kollero/Soldering-station/code/SRC/Thermotable.h

uint16_t Etype100amp[][2]={
{0,0},    
{12,10},  
{31,25},  
{50,40},  
{102,80}, 
{186,140},
{215,160},
{245,180},
{275,200},
{305,220},
{336,240},
{368,260},
{399,280},
{431,300},
{463,320},
{479,330},
{495,340},
{511,350},
{528,360},
{544,370},
{560,380},
{576,390},
{593,400},
{609,410},
{626,420},
{659,440},
{692,460},
{725,480},
{758,500}
};


//ADC value, then temperature calculated with gain of 100
uint16_t Ntype100amp[][2]={
{0,0},    
{13,25},  
{22,40},  
{45,80},  
{82,140}, 
{88,150}, 
{95,160}, 
{101,170},
{108,180},
{114,190},
{121,200},
{128,210},
{135,220},
{142,230},
{149,240},
{156,250},
{163,260},
{170,270},
{177,280},
{184,290},
{191,300},
{199,310},
{206,320},
{213,330},
{221,340},
{228,350},
{236,360},
{243,370},
{251,380},
{258,390},
{266,400},
{273,410},
{281,420},
{289,430},
{296,440},
{304,450},
{312,460},
{320,470},
{327,480},
{335,490},
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
};

uint16_t Ntype200amp[][2]={
{0,0},    
{27,25},  
{44,40},  
{90,80},  
{163,140},
{176,150},
{189,160},
{202,170},
{215,180},
{229,190},
{242,200},
{256,210},
{269,220},
{283,230},
{297,240},
{311,250},
{325,260},
{339,270},
{354,280},
{368,290},
{383,300},
{397,310},
{412,320},
{427,330},
{441,340},
{456,350},
{471,360},
{486,370},
{501,380},
{516,390},
{531,400},
{547,410},
{562,420},
{577,430},
{593,440},
{608,450},
{624,460},
{639,470},
{655,480},
{670,490},
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
};

//ADC value, C type then temperature calculated with gain of 500
//for 5V Vcc and 10-bit ADC, {adc,temp}
uint16_t Ctype500amp[][2]={
{0,0},    
{3,5},    
{18,25},  
{28,40},  
{59,80},  
{107,140},
{124,160},
{141,180},
{158,200},
{176,220},
{194,240},
{212,260},
{230,280},
{249,300},
{268,320},
{277,330},
{287,340},
{296,350},
{306,360},
{316,370},
{325,380},
{335,390},
{345,400},
{354,410},
{364,420},
{384,440},
{404,460},
{423,480},
{443,500}
};

uint16_t Stype1000amp[][2]={
{0,0},    
{11,10},  
{29,25},  
{48,40},  
{103,80}, 
{195,140},
{227,160},
{261,180},
{295,200},
{330,220},
{366,240},
{402,260},
{438,280},
{476,300},
{513,320},
{532,330},
{551,340},
{571,350},
{590,360},
{609,370},
{629,380},
{648,390},
{667,400},
{687,410},
{707,420},
{746,440},
{786,460},
{827,480},
{867,500}
};

uint16_t own500amp[][2]={
{0,25},   
{12,54},  
{34,99},  
{54,139}, 
{76,182}, 
{97,224}, 
{117,264},
{134,293},
{154,327},
{174,361},
{194,396},
{212,427},
{229,460},
{242,490},
{250,514}
};

uint16_t IrRh500amp[][2]={
{0,25},   
{14,40},  
{30,80},  
{56,140}, 
{86,200}, 
{108,240},
{130,280},
{141,300},
{153,320},
{165,340},
{177,360},
{189,380},
{201,400},
{213,420},
{238,460},
{263,500},
{294,550},
{325,600},
{387,700},
{506,900}
};
